teodor994/InkTime_project/Images/img1.png

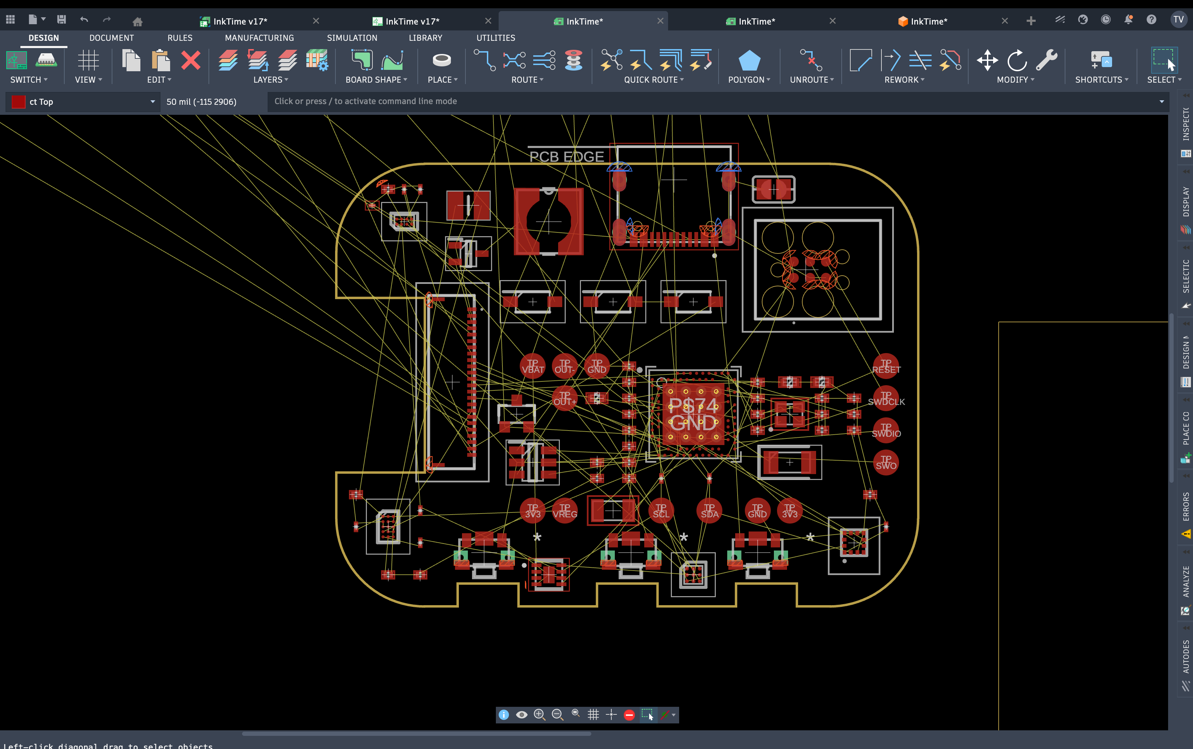
Images/img1.png
